Roukie686868/MultiSensor/Documents/Breadboard/Breadboard with headers1.jpg

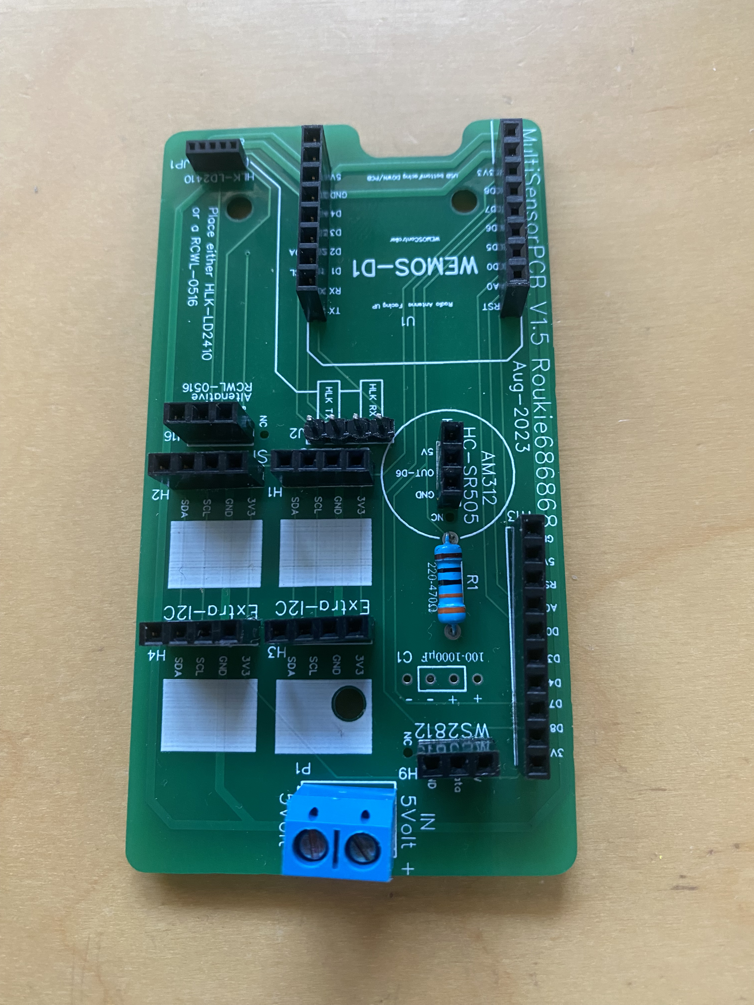
Documents/Breadboard/Breadboard with headers1.jpg
