Roukie686868/MultiSensor/Documents/Breadboard/Breadboard with headers2.jpg

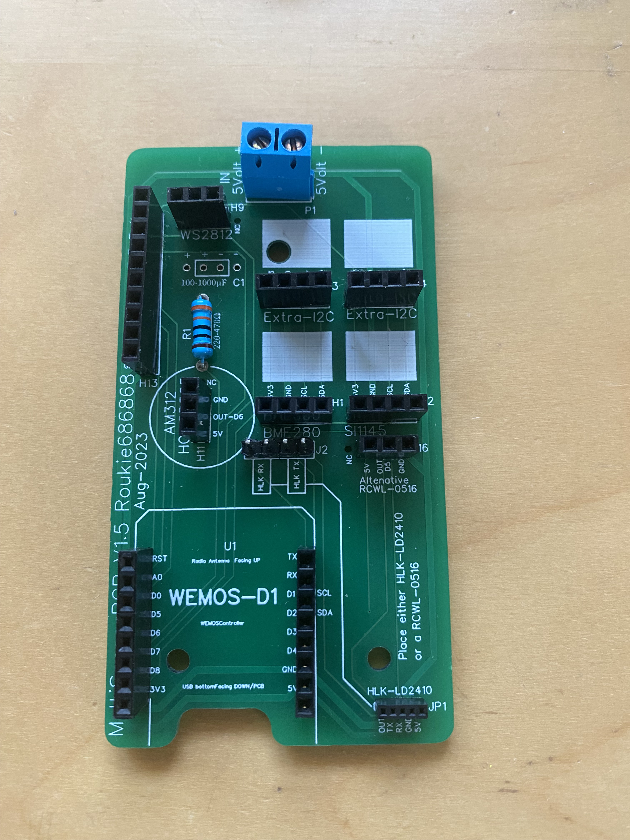
Documents/Breadboard/Breadboard with headers2.jpg
