Roukie686868/MultiSensor/Documents/Breadboard/Breadboard-V2 smallold.PNG

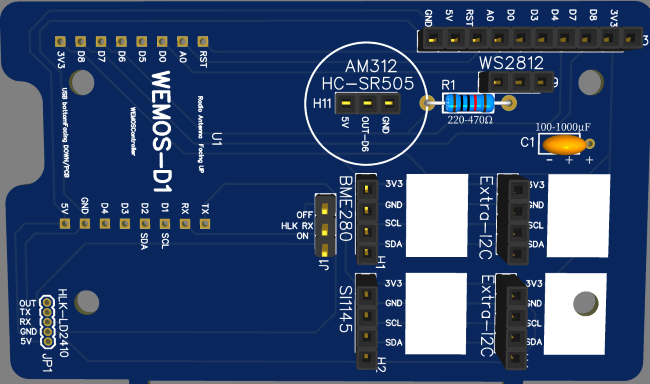
Documents/Breadboard/Breadboard-V2 smallold.PNG
