Roukie686868/MultiSensor/Documents/Breadboard/Breadboardsmall.PNG

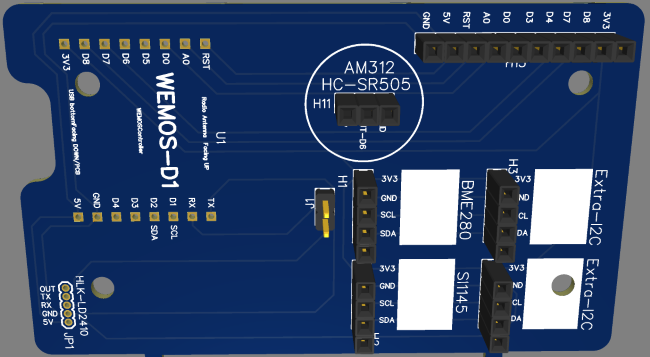
Documents/Breadboard/Breadboardsmall.PNG
