Roukie686868/MultiSensor/Documents/Breadboard/I2C-1.jpg

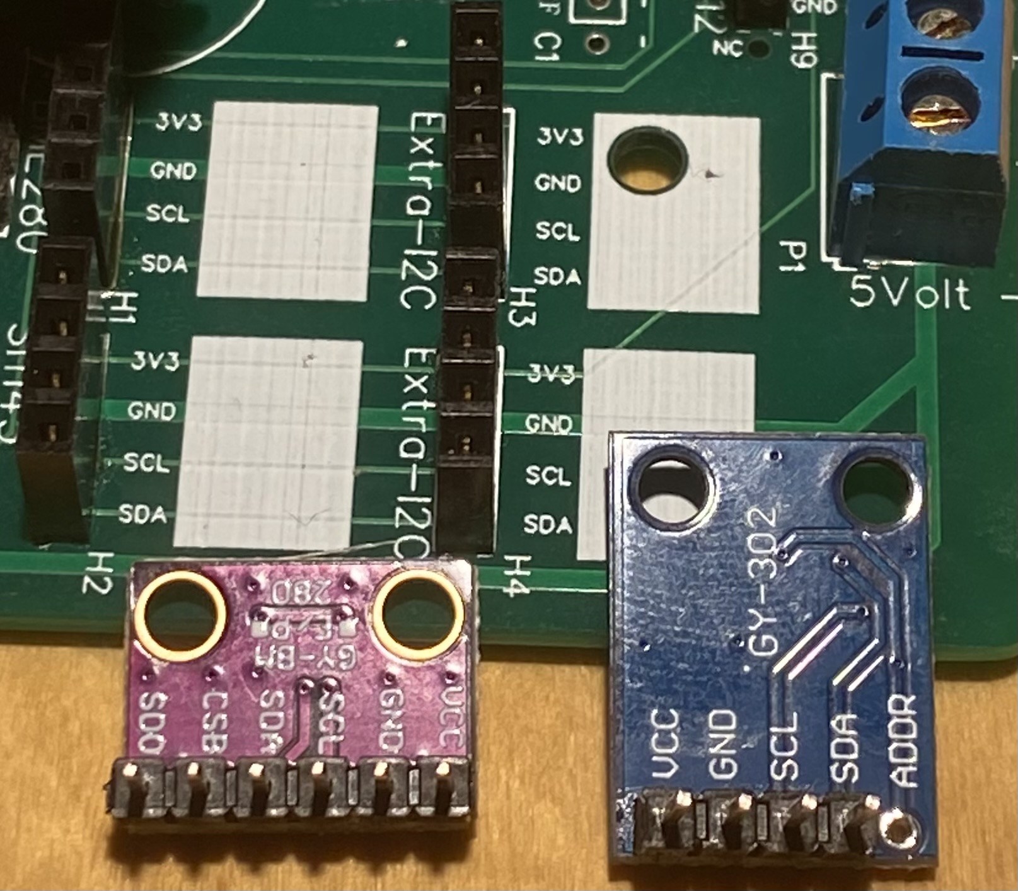
Documents/Breadboard/I2C-1.jpg
