Roukie686868/MultiSensor/Documents/Breadboard/I2C-2.jpg

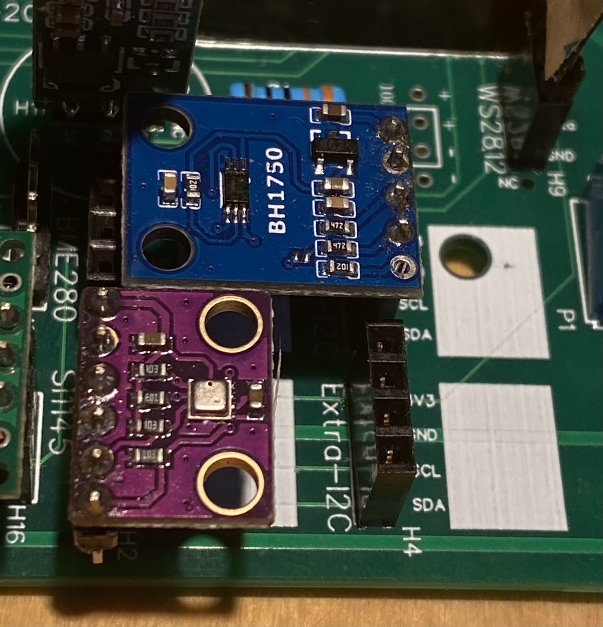
Documents/Breadboard/I2C-2.jpg
