Roukie686868/MultiSensor/Documents/Breadboard/I2C-3.jpg

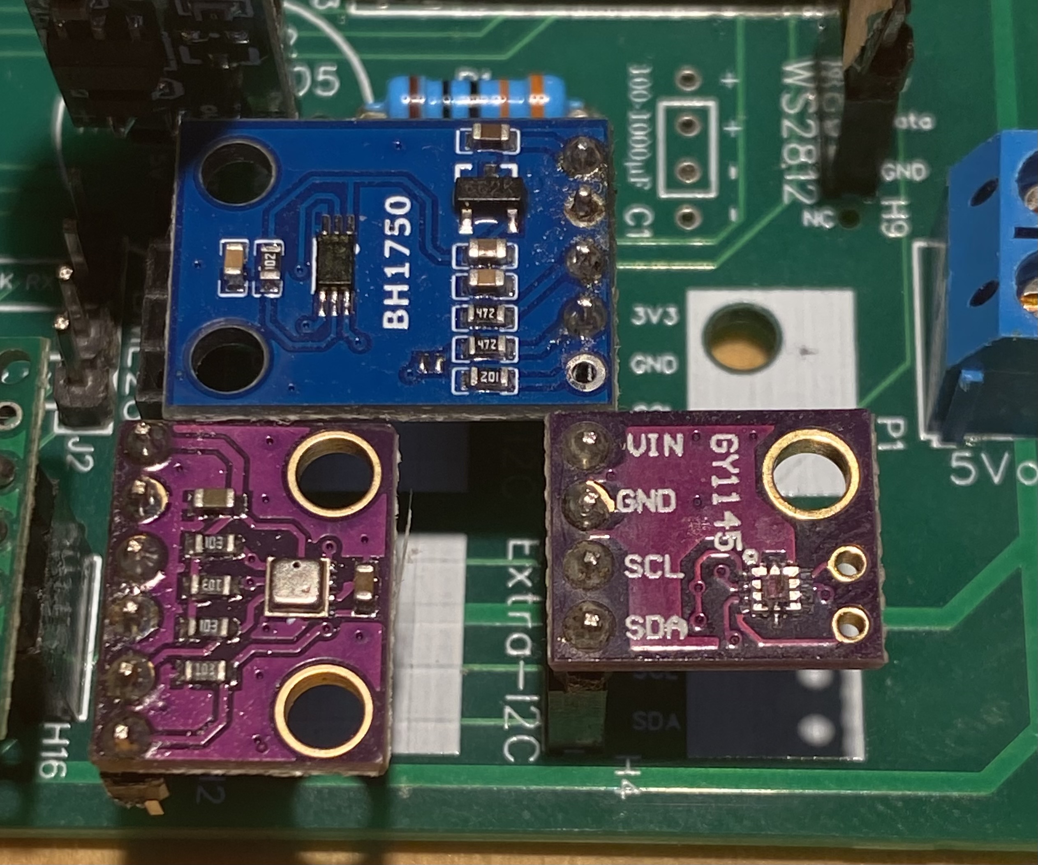
Documents/Breadboard/I2C-3.jpg
