Roukie686868/MultiSensor/Documents/Breadboard/RCWL-0516-1.jpg

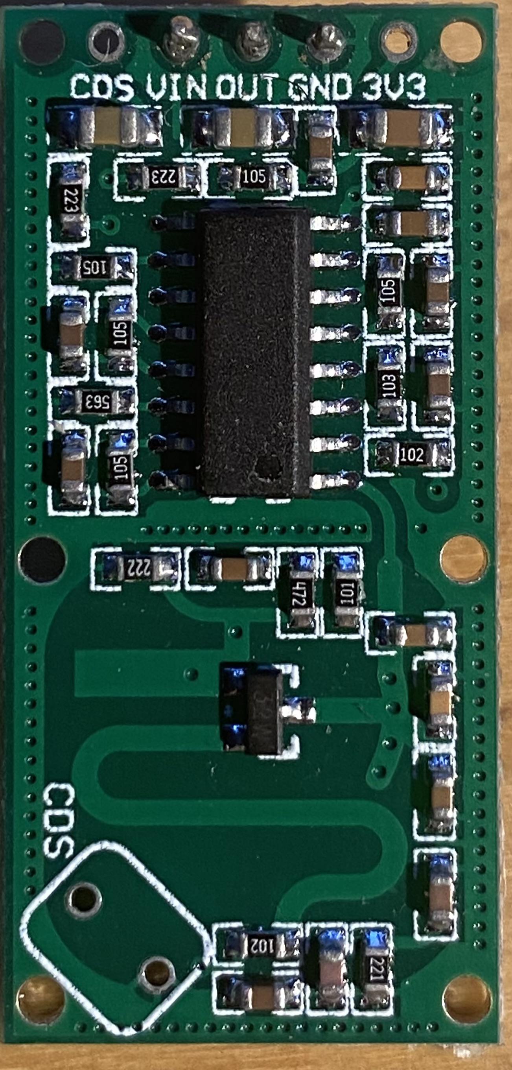
Documents/Breadboard/RCWL-0516-1.jpg
