Roukie686868/MultiSensor/Documents/Breadboard/RCWL-0516-2.jpg

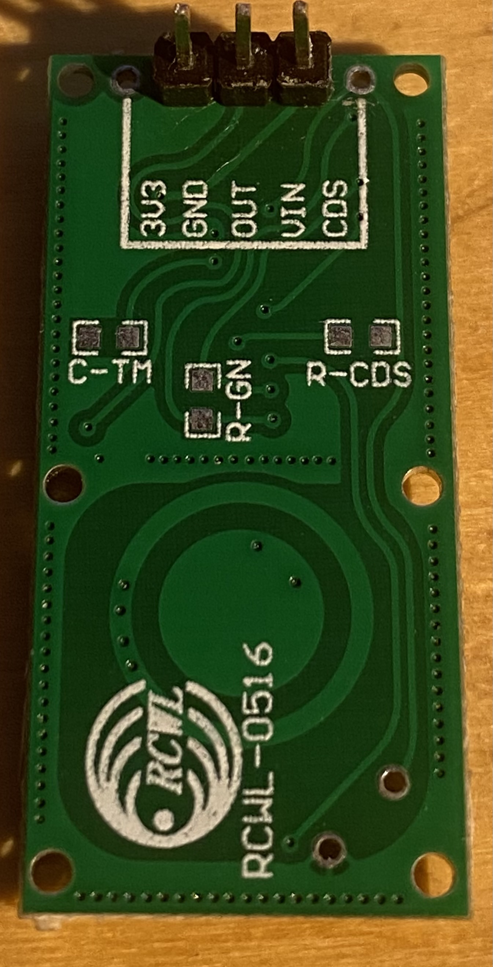
Documents/Breadboard/RCWL-0516-2.jpg
