Roukie686868/MultiSensor/Documents/Breadboard/RCWL-0516-3.jpg

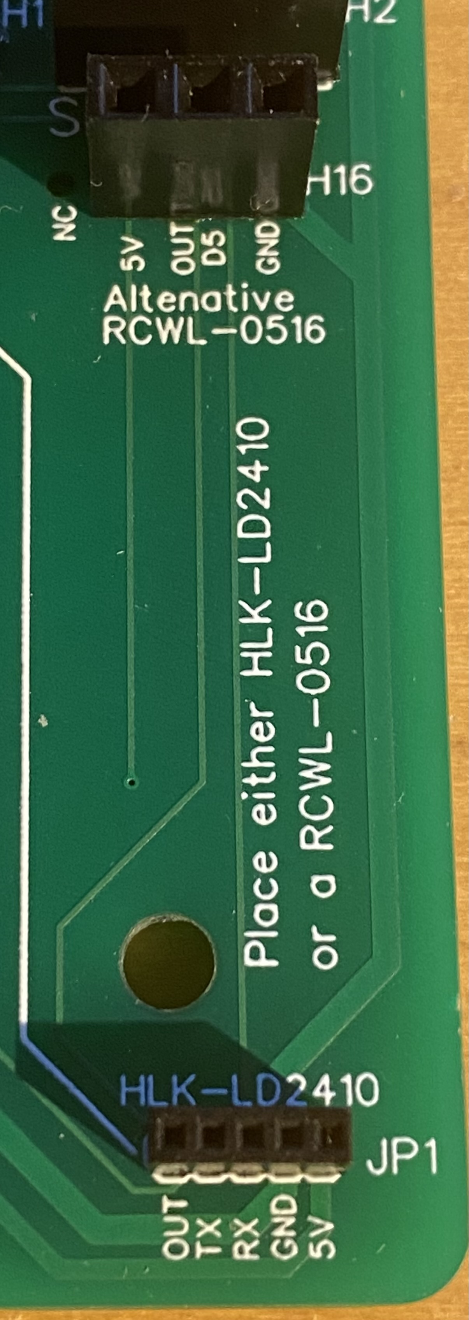
Documents/Breadboard/RCWL-0516-3.jpg
