Roukie686868/MultiSensor/Documents/Breadboard/SR505-1.jpg

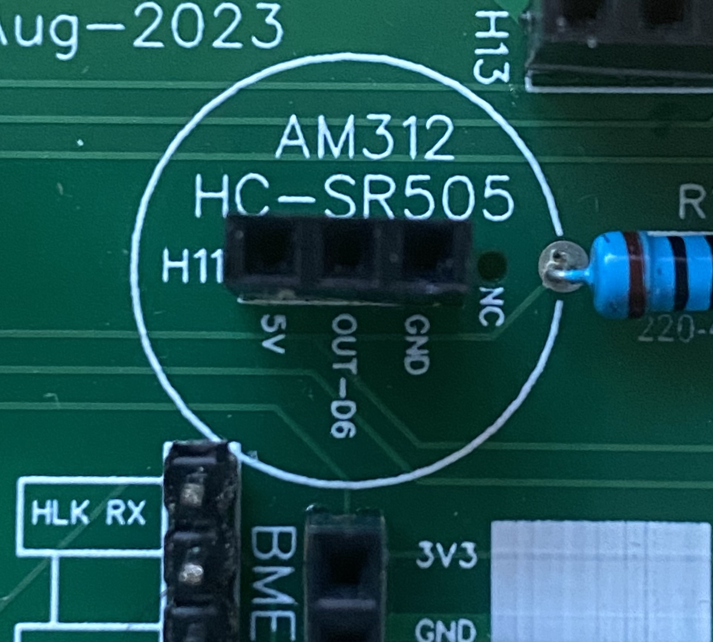
Documents/Breadboard/SR505-1.jpg
