Roukie686868/MultiSensor/Documents/Breadboard/SR505-2.jpg

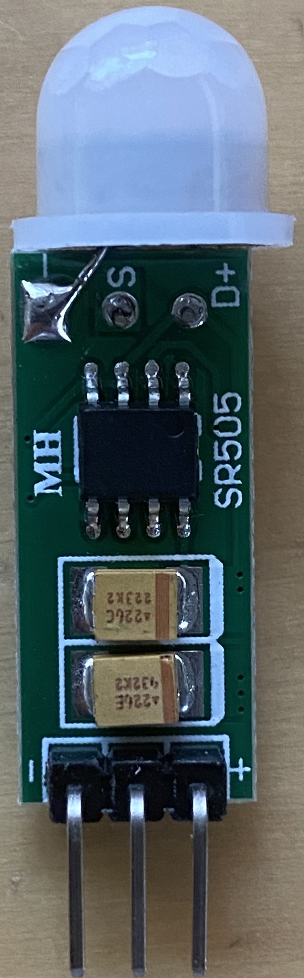
Documents/Breadboard/SR505-2.jpg
