Roukie686868/MultiSensor/Documents/Breadboard/SR505-3.jpg

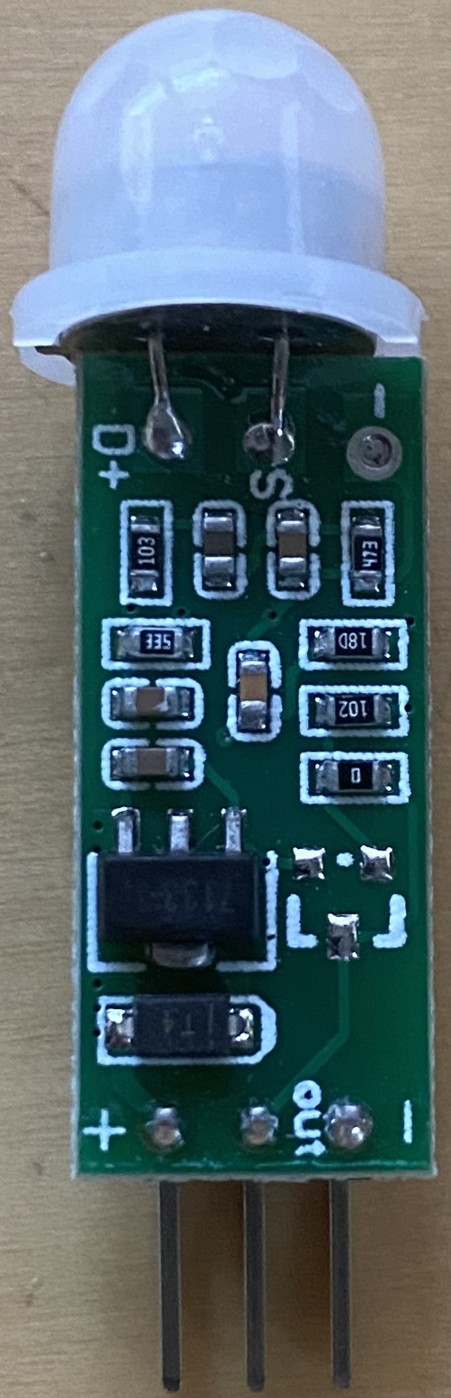
Documents/Breadboard/SR505-3.jpg
