Roukie686868/MultiSensor/Documents/Breadboard/Wemos-1.jpg

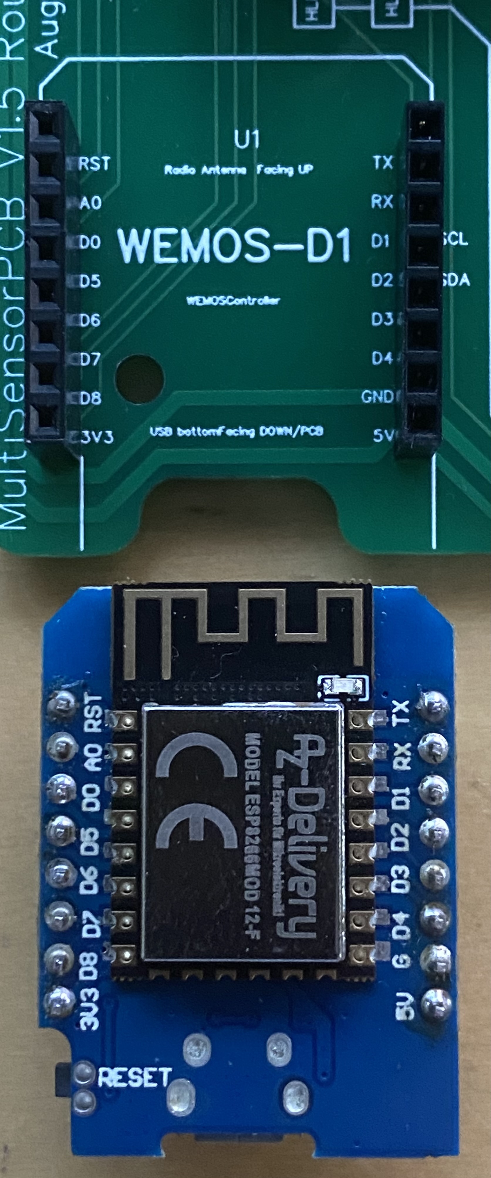
Documents/Breadboard/Wemos-1.jpg
