Roukie686868/MultiSensor/Documents/Breadboard/Wemos-2.jpg

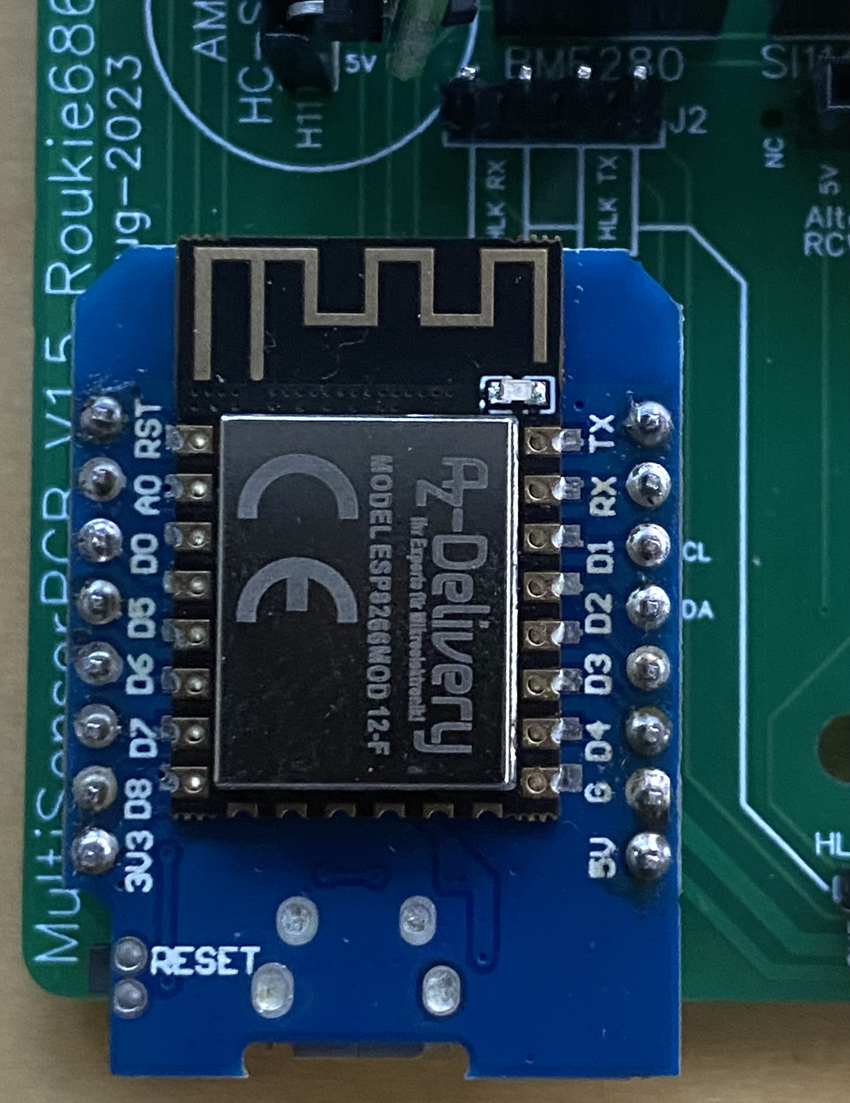
Documents/Breadboard/Wemos-2.jpg
