Roukie686868/MultiSensor/Documents/mmWave/HLK-LD2410/HLK-LD2410.PNG

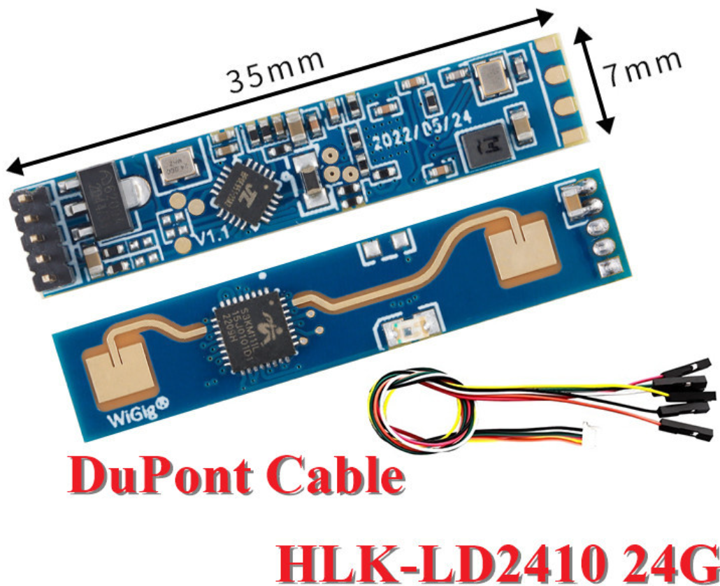
Documents/mmWave/HLK-LD2410/HLK-LD2410.PNG
