Roukie686868/MultiSensor/Documents/PIR/AM312-1.jpg

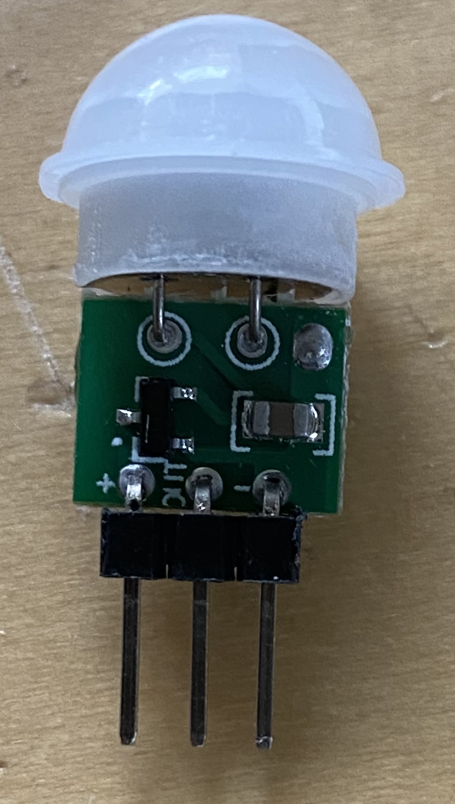
Documents/PIR/AM312-1.jpg
