Roukie686868/MultiSensor/Documents/PIR/AM312-2.jpg

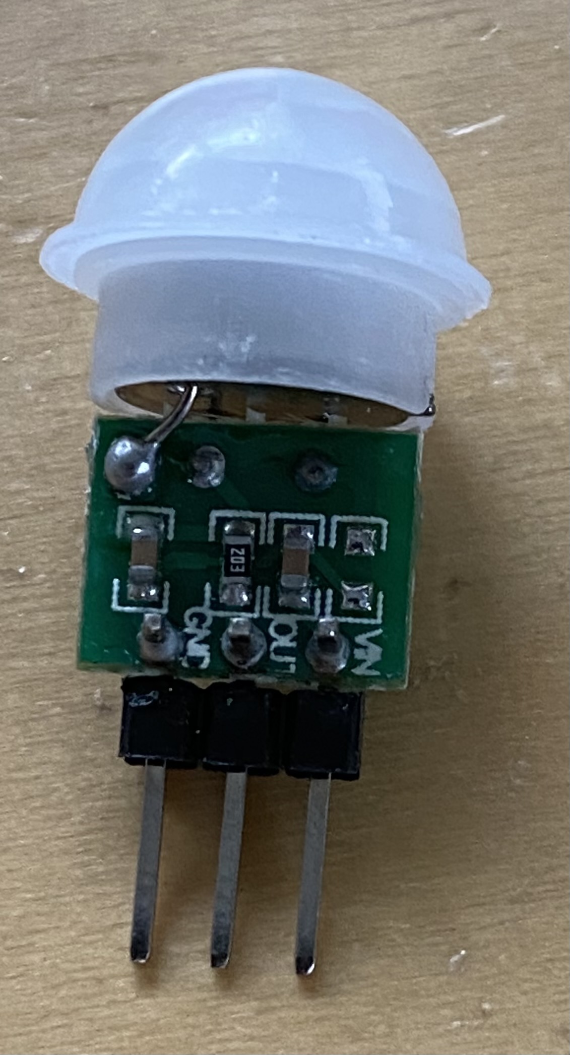
Documents/PIR/AM312-2.jpg
